eggcup001/BandaiCombat/artwork/png/ChatGPT Image.png

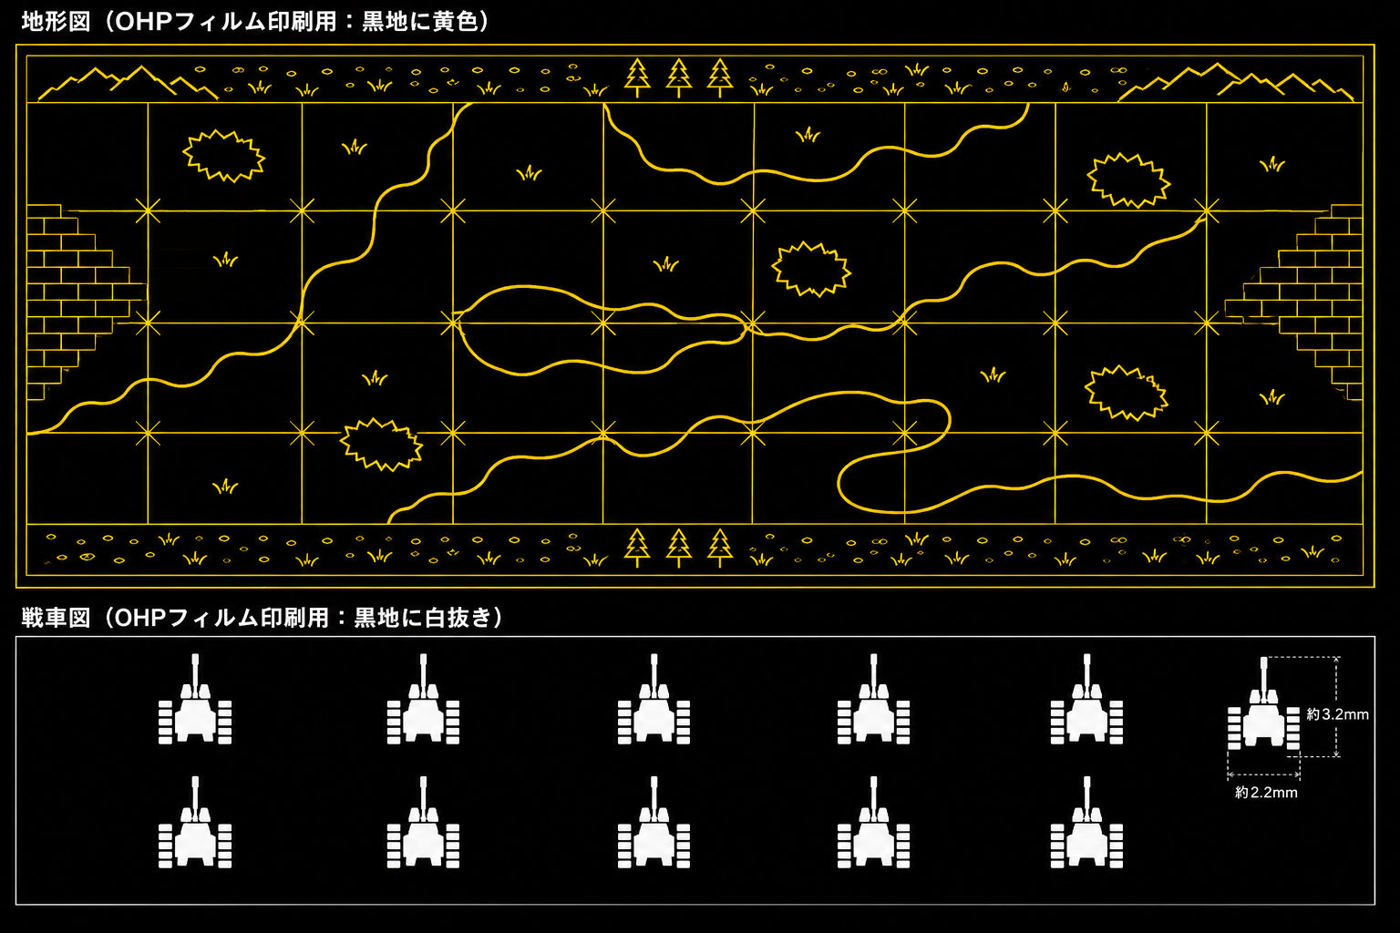
artwork/png/ChatGPT Image.png
