eggcup001/BandaiCombat/artwork/png/film_0.png

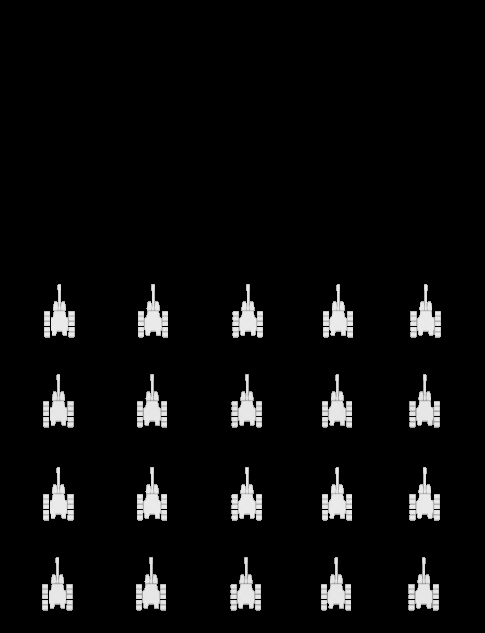
artwork/png/film_0.png
