eggcup001/BandaiCombat/artwork/png/film_1.png

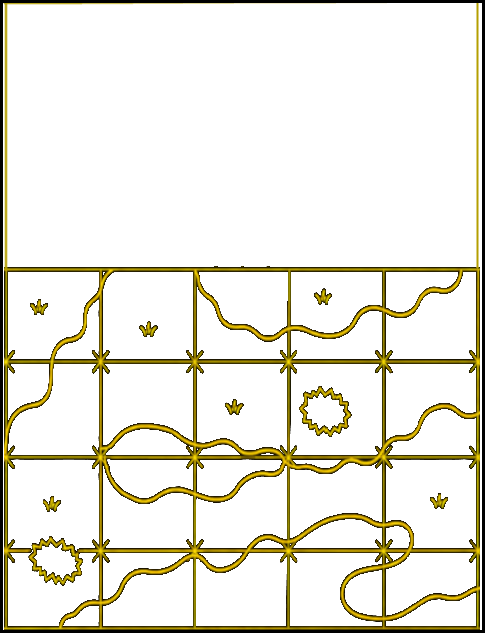
artwork/png/film_1.png
