eggcup001/BandaiCombat/docs/no1/002.png

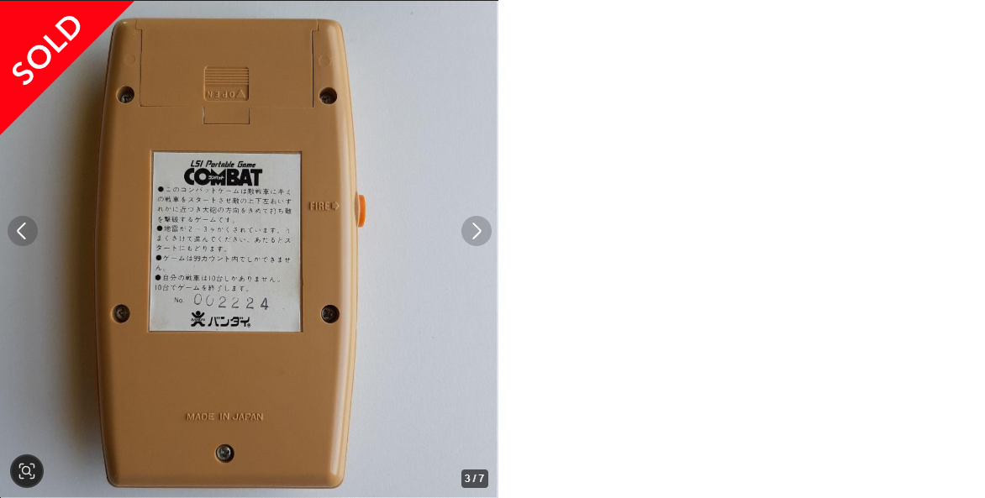
docs/no1/002.png
