eggcup001/BandaiCombat/docs/no1/003.png

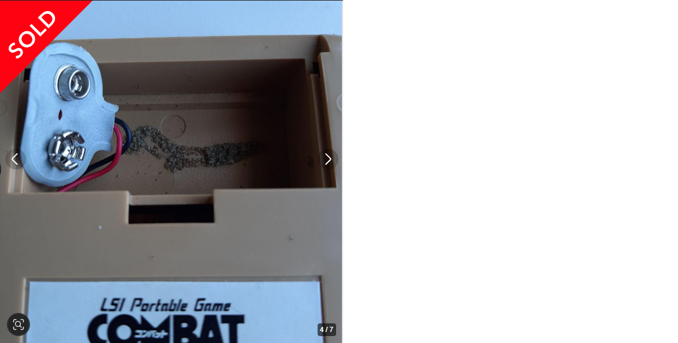
docs/no1/003.png
