eggcup001/BandaiCombat/docs/no2/001.png

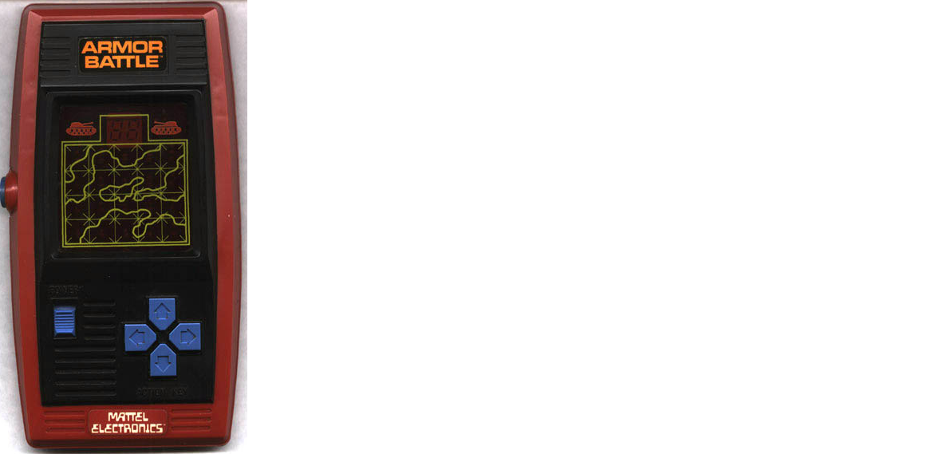
docs/no2/001.png
