eggcup001/BandaiCombat/docs/no3/スクリーンショット 2026-06-22 230106.png

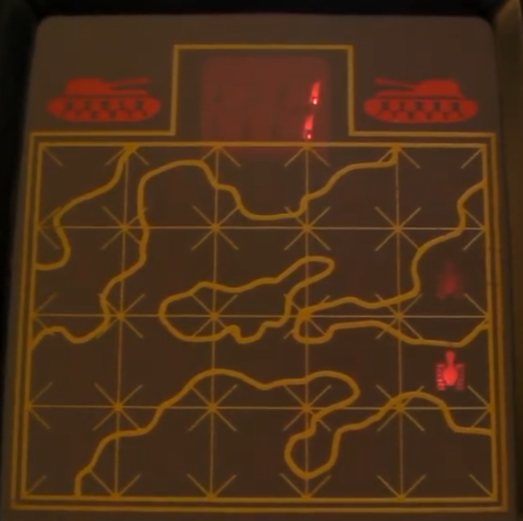
docs/no3/スクリーンショット 2026-06-22 230106.png
