eggcup001/BandaiCombat/docs/no4/260622115621873.JPG

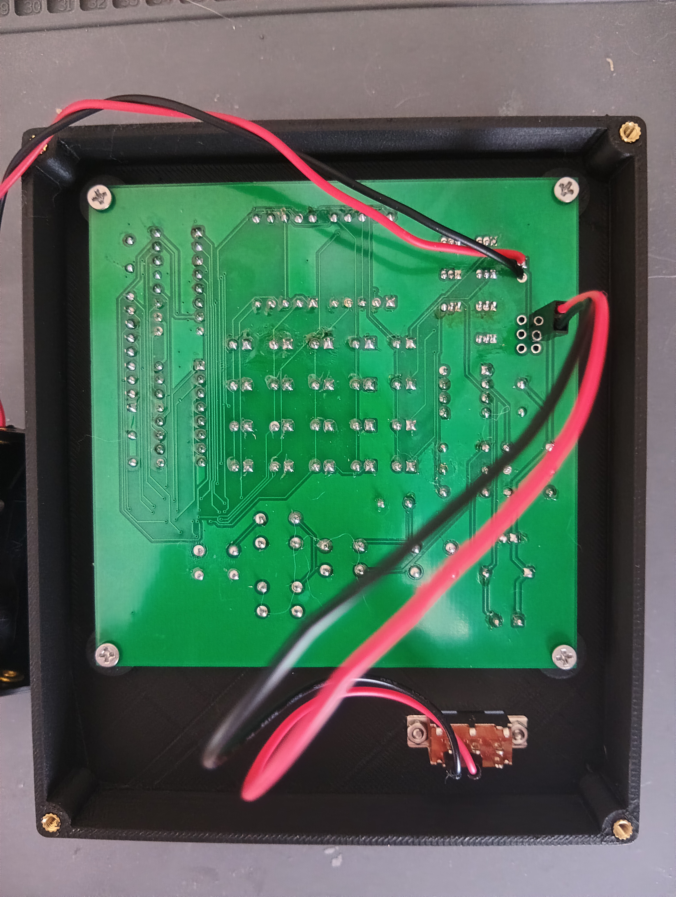
docs/no4/260622115621873.JPG
