eggcup001/BandaiCombat/docs/no4/260622115701737.JPG

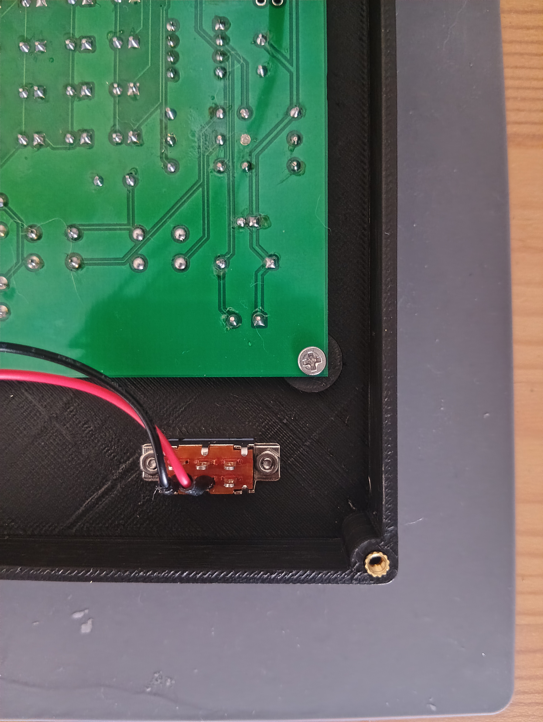
docs/no4/260622115701737.JPG
