eggcup001/BandaiCombat/docs/no4/260622115931212.JPG

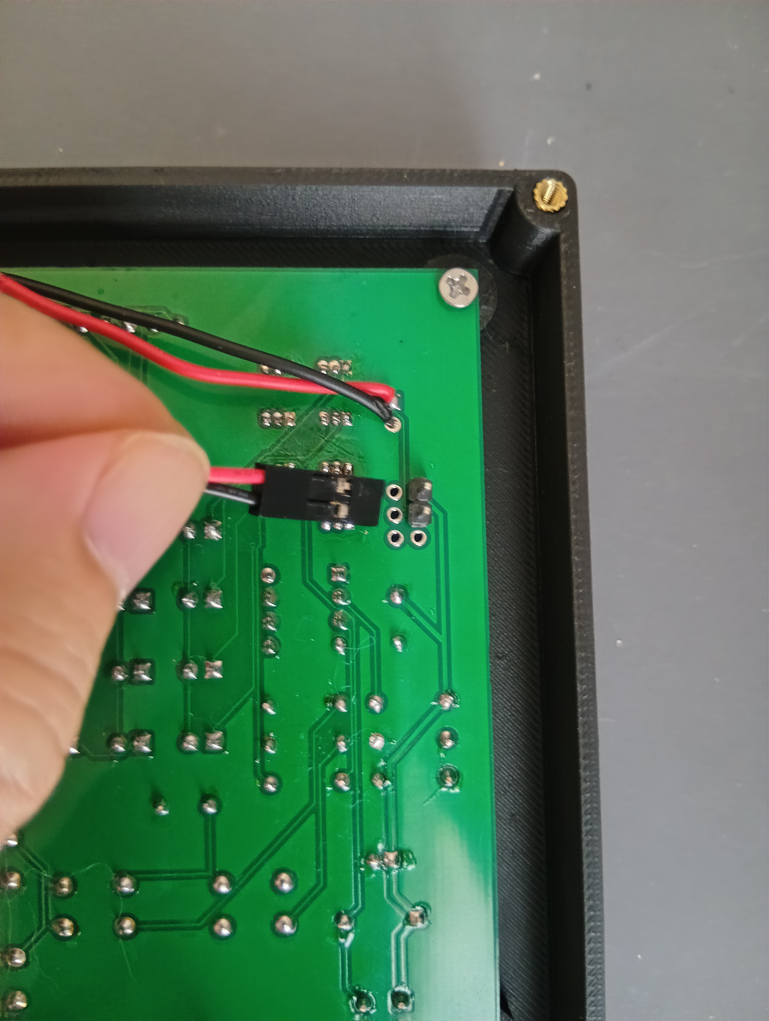
docs/no4/260622115931212.JPG
