eggcup001/BandaiCombat/docs/no4/260622130347687.JPG

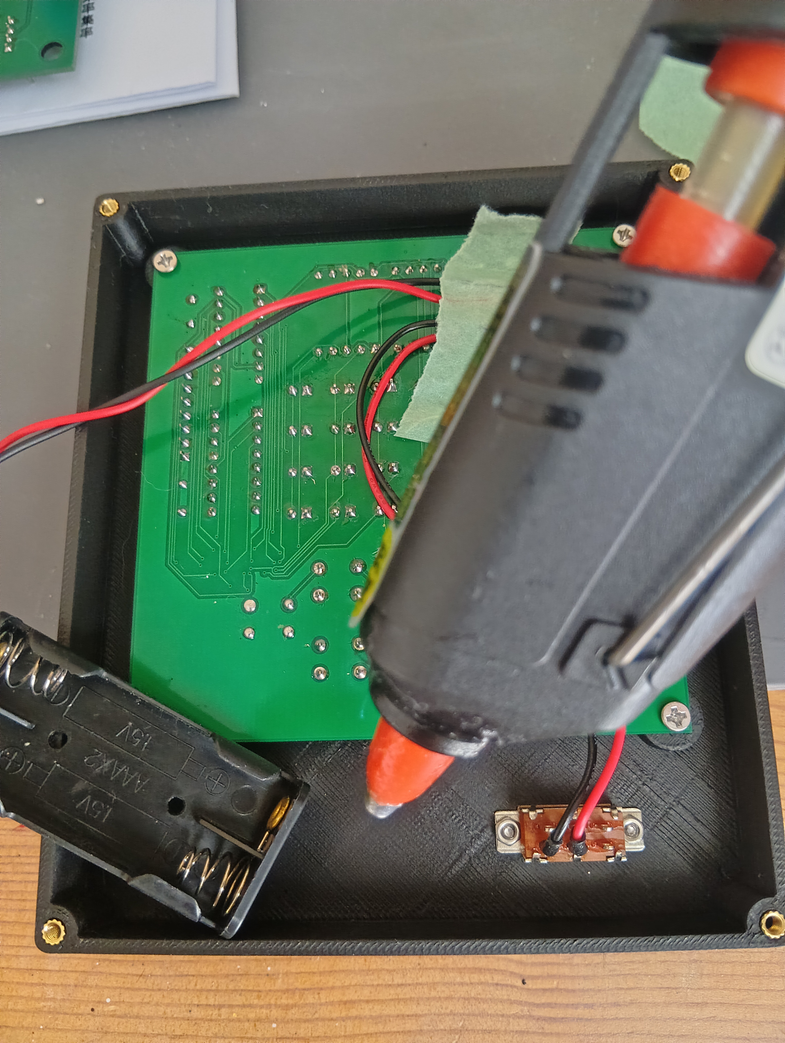
docs/no4/260622130347687.JPG
