eggcup001/BandaiCombat/docs/no4/260622130931173.JPG

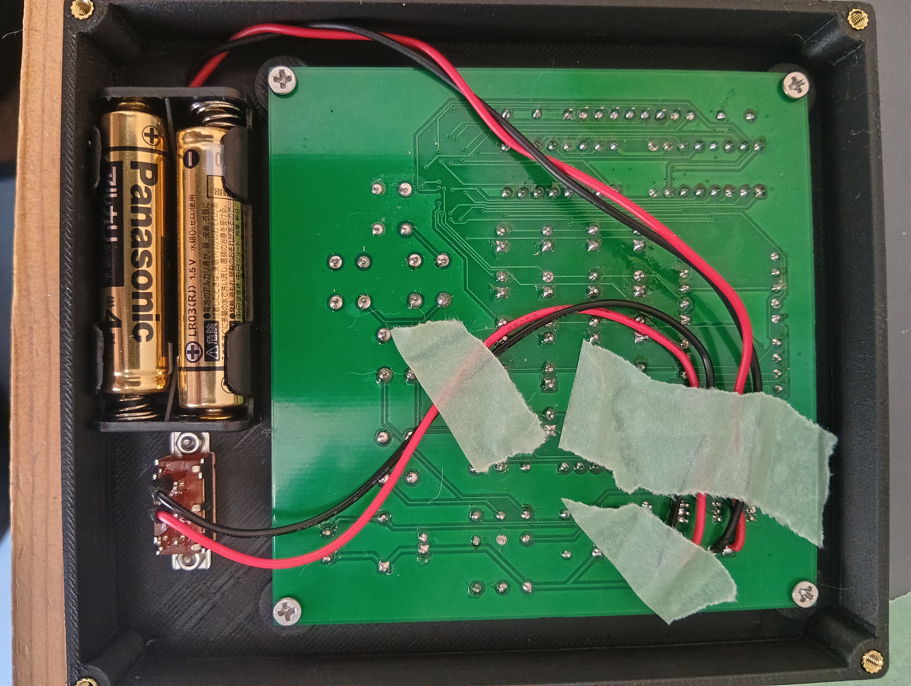
docs/no4/260622130931173.JPG
