eggcup001/BandaiCombat/docs/no4/260623170756172.JPG

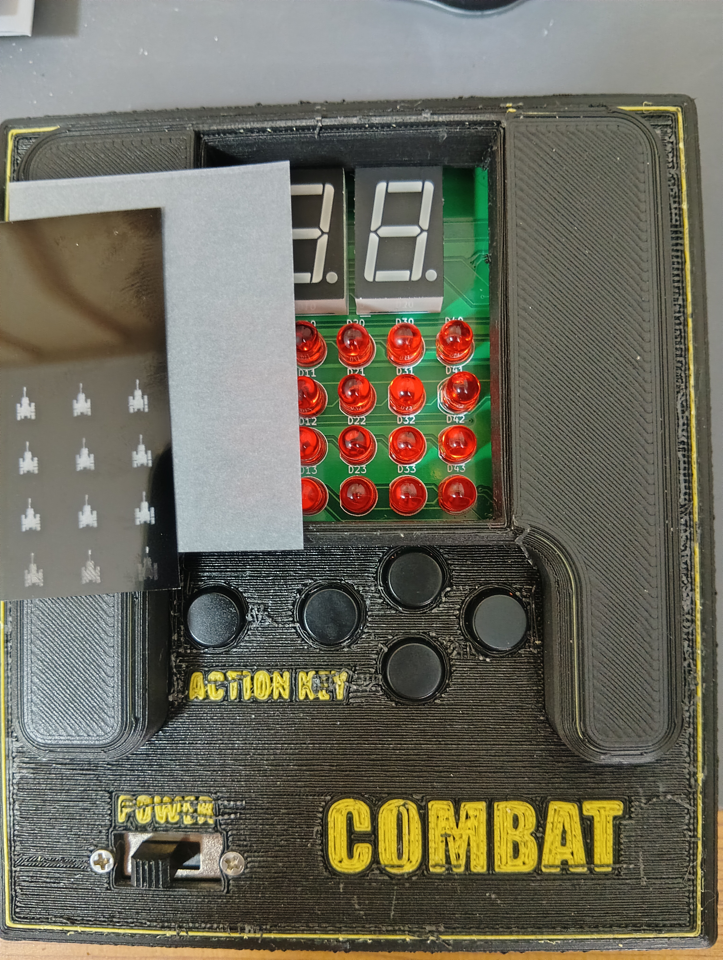
docs/no4/260623170756172.JPG
