eggcup001/BandaiCombat/docs/no4/260623170958922.JPG

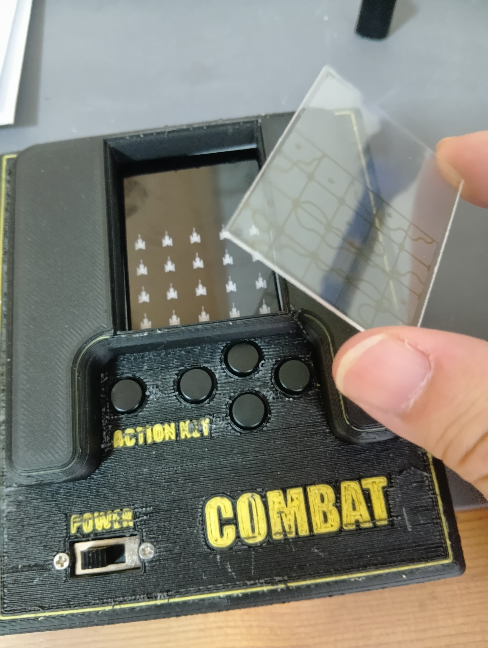
docs/no4/260623170958922.JPG
