eggcup001/BandaiCombat/docs/no4/260623171012706.JPG

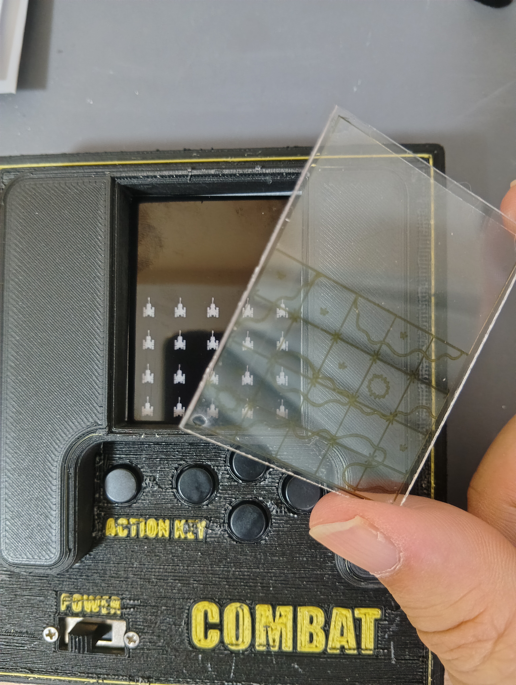
docs/no4/260623171012706.JPG
