eggcup001/BandaiCombat/docs/no4/260623171408021.JPG

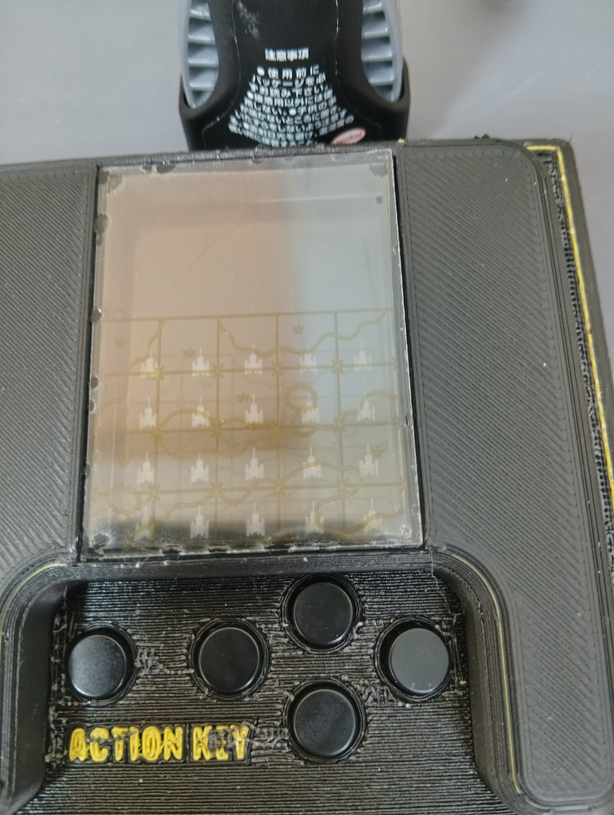
docs/no4/260623171408021.JPG
