eggcup001/BandaiCombat/docs/no4/260623172138746.JPG

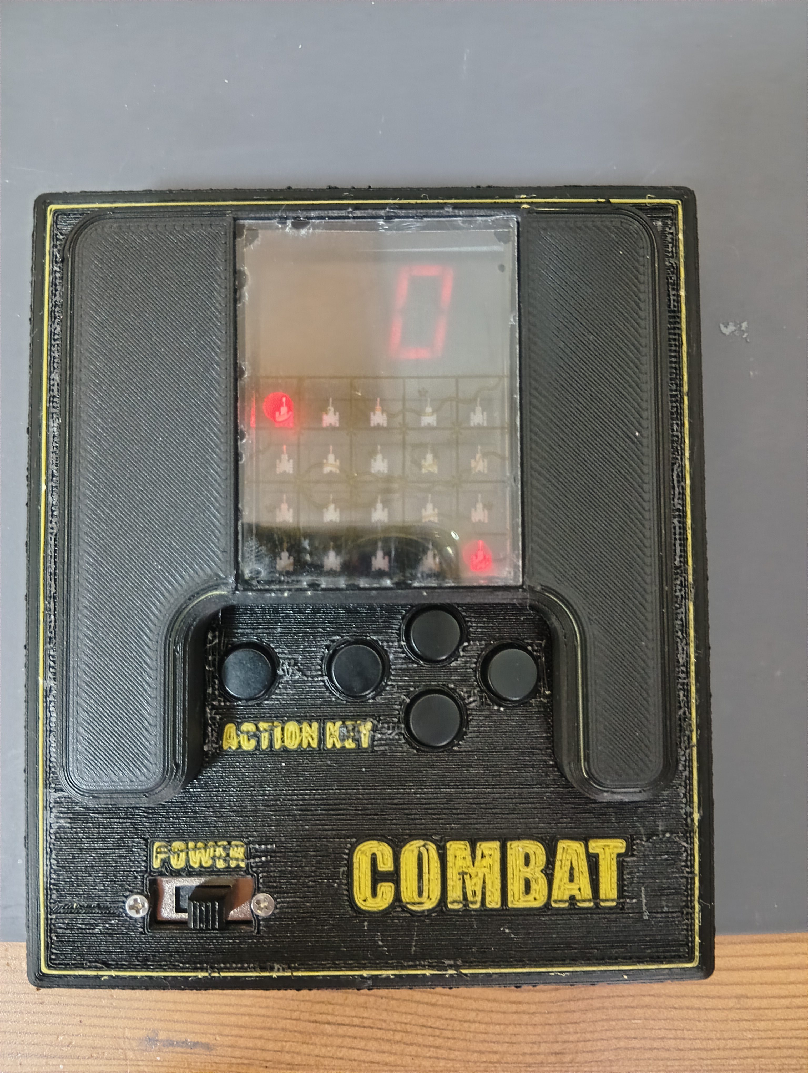
docs/no4/260623172138746.JPG
