eggcup001/BandaiCombat/docs/no4/260623172149741.JPG

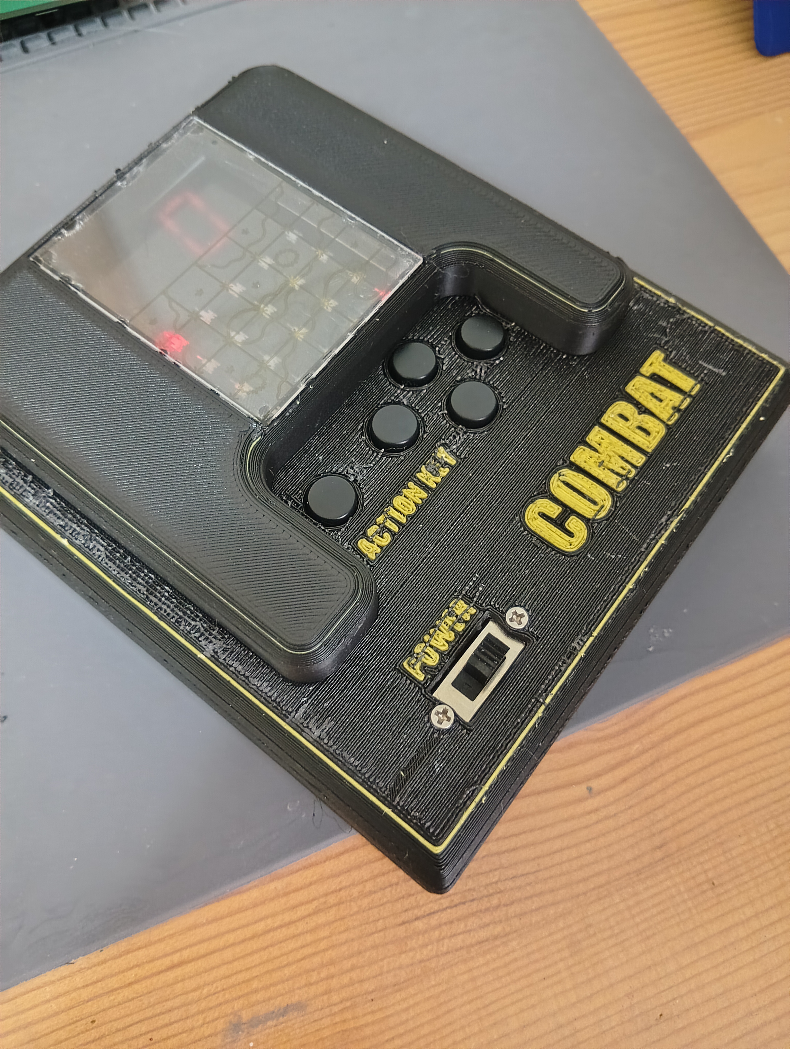
docs/no4/260623172149741.JPG
