eggcup001/BandaiCombat/docs/no4/260623172200967.JPG

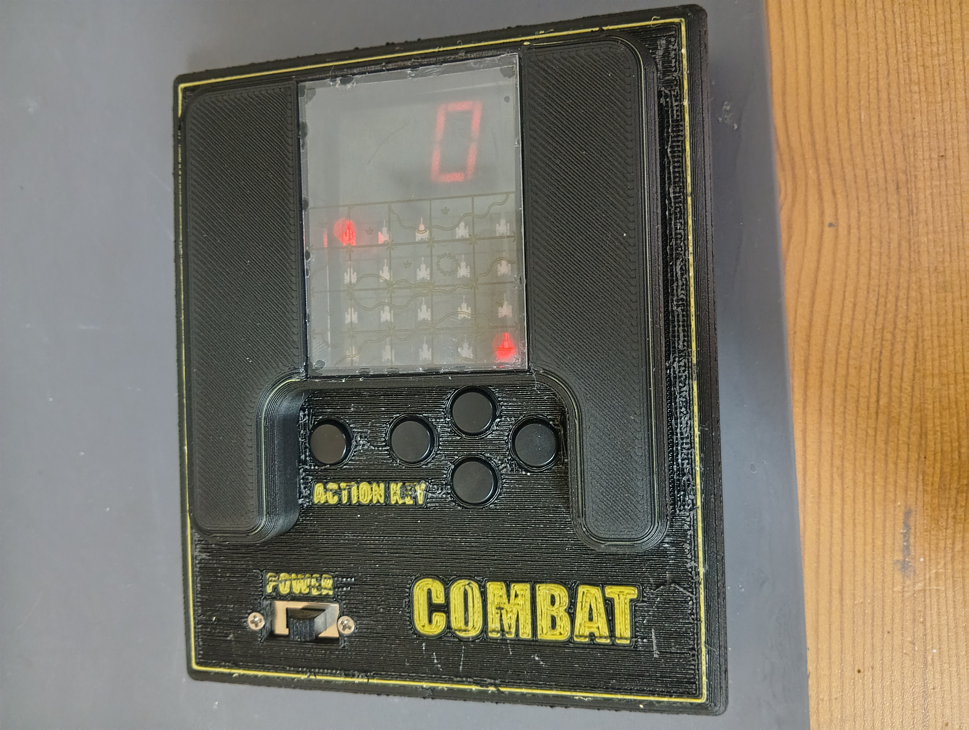
docs/no4/260623172200967.JPG
