eggcup001/BandaiCombat/docs/no4/260623171436803.JPG

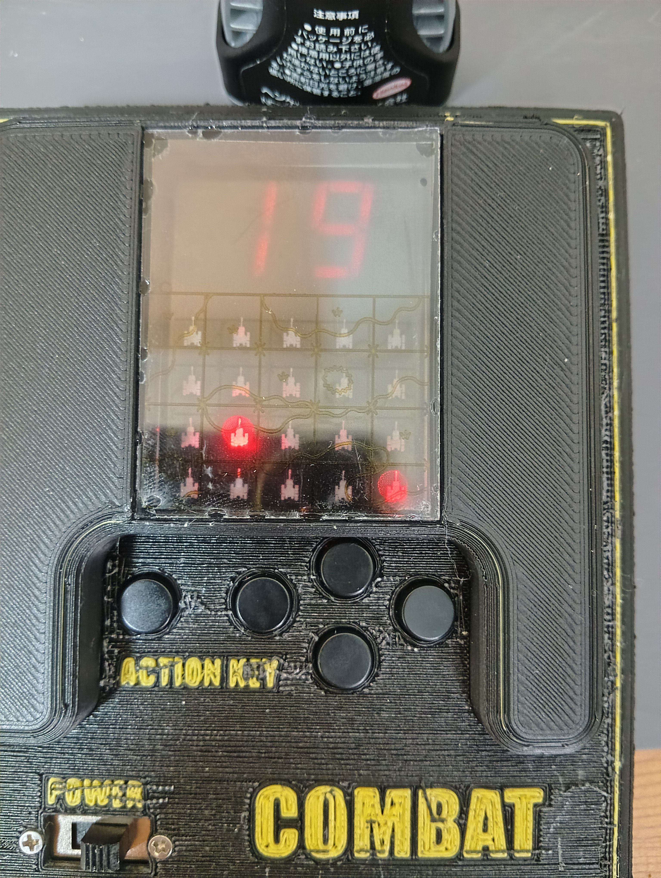
docs/no4/260623171436803.JPG
